idun-project/idun-cartridge/doc/330_112927.jpg

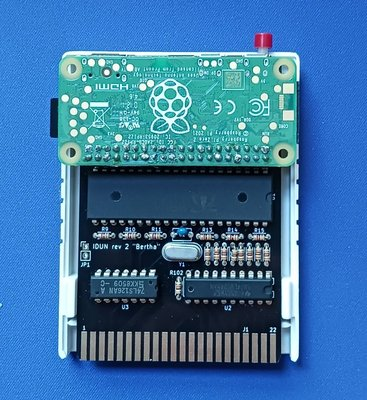
doc/330_112927.jpg
