idun-project/idun-cartridge/cbm/sys/acecall.asm

; Idun Kernel, Copyright ©2023 Brian Holdsworth
; This is free software, released under the MIT License.
;
; Original version from the ACE-128/64 system,
; by Craig Bruce, 1992-97 (http://csbruce.com/cbm/ace/)
;
; Main file/dir/other system calls

rtsErrIllegalDevice = *
   lda #aceErrIllegalDevice
   jmp rtsCarryErrno

;====== file calls ======

;*** open( zp=filenameZ, .A=mode["r","w","a","W","A"] ) : .A=fcb

aceOpenOverwrite = *
   +ldaSCII "w"
   jsr open
   bcs +
   rts
+  ldy errno
   cpy #aceErrFileExists
   beq +
   sec
-  rts
+  jsr internRemove
   bcs -
   bcc aceOpenWrite   ;.CC guaranteed here (fell through bcs above), effectively 2-byte jmp

aceOpenForceAppend = *
   +ldaSCII "a"
   jsr open
   bcs +
   rts
+  ldy errno
   cpy #aceErrFileNotFound
   beq aceOpenWrite
   sec
   rts

aceOpenWrite = *
   +ldaSCII "w"
   jmp kernFileOpen

;NAME   :  open
;PURPOSE:  open a file
;ARGS   :  (zp) = pathname
;          .A   = file mode ("r", "w", "a", "W", "A", or "C")
;RETURNS:  .A   = file descriptor number
;          .CS  = error occurred flag
;ALTERS :  .X, .Y, errno

openFcb      = syswork+0
openNameScan = syswork+1  ;mioCheckDiskStatus (acemiocbm.asm) reuses this byte
                          ;for its parsed status code once the name scan is done
openMode     = syswork+2
openNameLength = syswork+3
openDevice   = syswork+4
checkStat !byte 0

kernFileOpen = *
internOpen = *
   sta openMode
   +cmpASCII "W"
   bne +
   jmp aceOpenOverwrite
+  +cmpASCII "A"
   bne +
   jmp aceOpenForceAppend
+  +cmpASCII "C"
   bne ++
   jsr getFcb
   bcc +
   rts
+  +ldaSCII "R"
   sta openMode
   lda #cmdlf
   jmp fileOpenCont
++ jsr getLfAndFcb
   bcc fileOpenCont
   rts

   fileOpenCont = *
   sta lftable,x
   lda #$00
   sta eoftable,x
   sta checkStat
   stx openFcb
   jsr getDevice
   sty openNameScan
   ldx openFcb
   sta devtable,x
   sta openDevice
   tax
   ;get sa here
   lda configBuf+0,x
   ;** #0-#1 go to mio
   cmp #2
   bcs +
   jmp mioOpenSa
   ;** #2-#3: nothing else to do, just return the fcb
+  cmp #4
   bcs +
   lda openFcb
   ;clc not needed -- carry is guaranteed clear here (fell through bcs above)
   rts
   ;** check mem-mapper files
+  cmp #5
   bne +
   jmp internTagOpen
   ;** check virtual console
+  cmp #6
   bne +
   jmp pidOpen
   ; IDUN: type #4 and #7+ share this cmdlf/regsave dispatch --
   ; nothing else can reach here (0-3,5,6 all handled above)
+  ldx openFcb
   lda lftable,x
   cmp #cmdlf
   bne ++
   stx regsave+1
   ldx openDevice
   lda configBuf+2,x
   sta openFcb
   jsr pidOpen
   bcc +
   rts
+  lda regsave+1
   rts
++ jmp pidOpen

cmdchClose = *  ;( .X=device, matches cmdchOpen's convention )
   lda configBuf+0,x
   cmp #1
   bne +
   jmp mioCmdchClose
+  lda configBuf+2,x
   sta closeFd
   jmp pidClose


;NAME   :  close
;PURPOSE:  close an open file
;ARGS   :  .A   = File descriptor number
;RETURNS:  .CS  = error occurred flag
;ALTERS :  .A, .X, .Y, errno

closeFd !byte 0

kernFileClose = *
aceClose = *
internClose = *
   tax
   lda lftable,x
   cmp #cmdlf
   bne +
   lda devtable,x  ;cmdchClose now takes .X=device, translate fd->device here
   tax
   jmp cmdchClose
+  lda pidtable,x
   cmp aceProcessID
   beq +
   clc
   rts
+  ldy devtable,x
   stx closeFd
   internCloseCont = *
   lda configBuf+0,y
   ;** #0-#1 go to mio
   cmp #2
   bcs +
   jmp mioClosePath
   ;** #2-#3 just close entry
+  cmp #4
   bcs +
   bcc closeFdEntry ;.CC guaranteed here (fell through bcs above), effectively 2-byte jmp
   ;** check mem-mapper files
+  cmp #5
   bne +
   jsr internTagClose
   jmp closeFdEntry
   ;** IDUN virtual devices by now (type >=#4 except #5, including #6 virtual console)
+  jsr pidClose
   ; fall through to closeFdEntry

   closeFdEntry = *
   ldx closeFd
   lda #lfnull
   sta lftable,x
   clc
   rts

;NAME   :  read
;PURPOSE:  read data from an open file
;ARGS   :  .X   = File descriptor number
;          (zp) = pointer to buffer to store data into
;          .AY  = maximum number of bytes to read
;RETURNS:  .AY  = (zw) = number of bytes actually read in
;          .CS  = error occurred flag
;          .ZS  = EOF reached flag
;ALTERS :  .X, errno

readMaxLen     = syswork+0
readPtr        = syswork+2
readLength     = syswork+6
readFcb        = syswork+8
readDeviceDisk = syswork+9

;*** read( .X=fcb, (zp)=data, .AY=maxLength ) : .AY=(zw)=length, .Z=eof
kernFileRead = *
   sta readMaxLen+0
   sty readMaxLen+1
   stx readFcb
   lda zp+0
   ldy zp+1
   sta readPtr+0
   sty readPtr+1
   lda #0
   sta readLength+0
   sta readLength+1
   lda eoftable,x
   beq +
   jmp readEofExit
+  lda devtable,x
   tax
   lda configBuf+0,x
   ;** #0-#1 go to mio
   cmp #2
   bcs +
   jmp mioReadPath
   ;** check #2 console
+  cmp #2
   bne +
   lda readMaxLen+0
   ldy readMaxLen+1
   ldx readFcb
   jmp conRead
   ;** check #3 null device
+  cmp #3
   bne +
   lda #0
   ldy #0
   sta zw+0
   sty zw+1
   clc
   rts
   ;** check mem-mapper files
+  cmp #5
   bne +
   jmp internTagRead
   ;** check virtual console -- not implemented for read
+  cmp #6
   bne +
   jmp rtsErrIllegalDevice
   ;** IDUN virtual devices (type #4, #7+); nothing else can reach here
+  jmp pidRead

   readEofExit = *
   lda #0
   ldy #0
+  sta zw+0
   sty zw+1
   clc
   rts


;NAME   :  write
;PURPOSE:  write data to an open file
;ARGS   :  .X   = file descriptor number
;          (zp) = pointer to data to be written
;          .AY  = length of data to be written in bytes
;RETURNS:  .CS  = error occurred
;ALTERS :  .A, .X, .Y, errno

writeLength = syswork+0
writePtr    = syswork+2

;*** write( .X=fcb, (zp)=data, .AY=length )
kernFileWrite = *
internWrite = *
   sta writeLength+0
   sty writeLength+1
   lda zp+0
   ldy zp+1
   sta writePtr+0
   sty writePtr+1
   stx regsave+1
   lda devtable,x
   tax
   lda configBuf+0,x
   ;** #0-#1 go to mio
   cmp #2
   bcs +
   jmp mioWritePath
   ;** check console
+  cmp #2
   bne +
   lda writeLength+0
   ldy writeLength+1
   ldx regsave+1
   jmp conWrite
   ;** check null device
+  cmp #3
   bne +
   clc
   rts
   ;** #5-#6: mem-mapper files/virtual console, neither implemented for write;
+  cmp #5
   bcc +
   cmp #7
   bcs +
   jmp rtsErrIllegalDevice
   ;** everything else (type #4, #7+) goes to pidWrite
+  ldx regsave+1
   jmp pidWrite

;NAME   :  seek
;PURPOSE:  seek to file location
;ARGS   :  .X   = file descriptor number
;          .AY  = desired seek offset from start-of-file
;RETURNS:  .CS  = error occurred
;ALTERS :  .A, .X, .Y, errno

seekPtr       = syswork+0

;*** seek( .X=fcb, .AY=offset )

kernFileLseek = *
   sta seekPtr+0
   sty seekPtr+1
   ldy #0
   lda devtable,x
   tax
   lda configBuf+0,x
   ;seek only suppoorted by mem-mapped files (#5)
   cmp #5
   bne lseekIllegal
   jmp internTagSeek
   lseekIllegal = *
   jmp rtsErrIllegalDevice


;NAME   :  aceFileRemove
;PURPOSE:  delete a file
;ARGS   :  (zp) = pathname
;RETURNS:  .CS  = error occurred flag
;ALTERS :  .A, .X, .Y, errno

removeDevice = syswork+0  ;== renameDevice/chdirDevice below -- acemiocbm.asm's
                           ;mioCmdchTransact relies on this shared location to
                           ;fold its open/send/status/close tail across
                           ;mioRemovePath, mioRenamePath and mioChdirPath
;openNameScan(syswork+1) is set below too, then reused by mioCheckDiskStatus
;for its status code once mioRemovePath has consumed it -- see acemiocbm.asm

;*** aceFileRemove( (zp)=Name )
kernFileRemove = *
internRemove = *
   jsr getDiskDevice     ;bails out of this call on non-disk device
   sta removeDevice
   sty openNameScan
   ; IDUN: Type #1. Call MOS
   cpx #1
   bne +
   jmp mioRemovePath
   ; IDUN: Type #4/7. Replace with acepid.
+  ldx removeDevice
   jmp pidRemove


;NAME   :  aceFileRename
;PURPOSE:  rename a file or directory
;ARGS   :  (zp) = old filename
;          (zw) = new filename
;RETURNS:  .CS  = error occurred flag
;ALTERS :  .A, .X, .Y, errno

renameDevice = syswork+0  ;== removeDevice above/chdirDevice below -- see the
                           ;mioCmdchTransact note at removeDevice's definition
;openNameScan(syswork+1) is set below too, then reused by mioCheckDiskStatus
;for its status code once mioRenamePath has consumed it -- see acemiocbm.asm

;*** aceFileRename( (zp)=OldName, (zw)=NewName )
;*** don't even think about renaming files outside the current directory
kernFileRename = *
   jsr getDiskDevice     ;bails out of this call on non-disk device
   sta renameDevice
   sty openNameScan
   ; IDUN: Type #1. Call MOS
   cpx #1
   bne +
   jmp mioRenamePath
   ; IDUN: Type #4/7. Replace with acepid.
+  ldx renameDevice
   jmp pidRename


;NAME   :  aceFileBload/aceFileBkload
;PURPOSE:  binary load
;ARGS   :  .X   = RAM bank (0-3 *aceFileBkload only*)
;          (zp) = pathname
;          .AY  = address to load file
;          (zw) = highest address that file may occupy, plus one
;RETURNS:  .AY  = end address of load, plus one
;          .CS  = error occurred flag
;ALTERS :  .X, errno
bloadAddress = syswork
bloadFilename= syswork+2
bloadDevice  = syswork+8
bloadBank    = syswork+9

;*** aceFileBkload( .X=Bank (zp)=Name, .AY=Address, (zw)=Limit+1 ) : .AY=End+1
kernFileBkload = *
internBkload = *
   stx bloadBank
   ldx #0
   jmp +
;*** aceFileBload( (zp)=Name, .AY=Address, (zw)=Limit+1 ) : .AY=End+1
kernFileBload = *
internBload = *
   ldx #0
   stx bloadBank
+  stx checkStat
   stx BloadAppflag
   sta bloadAddress+0
   sty bloadAddress+1
   jsr getDevice
   sta bloadDevice
   tax
   clc
   tya
   adc zp+0
   sta bloadFilename+0
   lda zp+1
   adc #0
   sta bloadFilename+1
   ;IDUN: Check prog name not NUL
   ldy #0
   lda (bloadFilename),y
   bne +
   lda #aceErrFileNotFound
   jmp rtsCarryErrno
+  lda configBuf+0,x
   ;** #1 -> mio
   cmp #1
   bne +
   jmp mioBloadPath
   ;** #5 -> tag RAM
+  cmp #5
   bne +
   jmp internTagBload
   ;** #4/#7 -> pid
+  cmp #4
   beq +
   cmp #7
   bne ++
+  jmp pidBload
++ jmp rtsErrIllegalDevice

;*** aceDirStat ( .A=stat, (zp)=path ) : CS=error,errno
;                                .CC=filled aceSharedBuf

miscInfoDevice = syswork+1  ;kernMiscDeviceInfo's (below) returned device
                            ;number; every caller (here, kernFileStat, and
                            ;mioFileStat in acemiocbm.asm) reads it right
                            ;back out before this slot goes back to being
                            ;openNameScan/chdirNameScan. Defined here, ahead
                            ;of kernMiscDeviceInfo's own definition, so ACME
                            ;sees it as zero page from its first use instead
                            ;of sizing a forward-referenced load as absolute
kernDirStat = *
   ldx #"/"
   cmp #$80
   bne +
   ldx #"%"
+  stx cmdPrefix
   jsr kernMiscDeviceInfo
   bcs +
   jmp rtsErrIllegalDevice
+  lda miscInfoDevice
   sta openDevice
   lda #"r"
   sta openMode
   sty openNameScan
   jsr pidCommandSend
   lda #<dstatRespHandler
   ldy #>dstatRespHandler
   jmp pidCommandResponse
dstatRespHandler = *
   jsr pidFlushbuf
   ; UNLISTEN
   lda #$3F
   jsr pidChOut
   ; Read response size
-  jsr pidChIn
   bcs -
   beq +
   tax
   lda #<aceSharedBuf
   ldy #>aceSharedBuf
   jsr kernModemGet
   lda #$00
+  sta aceSharedBuf,x
   rts

;*** aceFileStat ( (zp)=path ) : .AY=file size,.CS=error,errno
;                                .CC=filled aceDirentBuffer

kernFileStat = *
   jsr kernMiscDeviceInfo
   bcc mioFileStatEntry
   lda miscInfoDevice
   sta openDevice
   lda #"r"
   sta openMode
   lda #"#"
   sta cmdPrefix
   sty openNameScan
   jsr pidCommandSend
   lda #<fstatRespHandler
   ldy #>fstatRespHandler
   jmp pidCommandResponse
fstatRespHandler = *
   jsr pidFlushbuf
   ; UNLISTEN
   lda #$3F
   jsr pidChOut
   ; Read response
   lda #<aceDirentBuffer
   ldy #>aceDirentBuffer
   ldx #aceDirentLength
   jsr kernModemGet
   lda aceDirentNameLen
   bne +
   sec
   rts
+  lda aceDirentBytes+0
   ldy aceDirentBytes+1
   rts

;-- fstatFcb: scratch shared with mioFileStat (acemiocbm.asm); kernDirRead
;   does not touch syswork+3
fstatFcb = syswork+3
mioFileStatEntry = *
   jmp mioFileStat

;-- fcbSetup: allocate FCB; fill lftable/devtable/eoftable/satable/openFcb
;   ( openDevice=set ) : .X=fcb, .CS=error
fcbSetup = *
   jsr getLfAndFcb
   bcs +
   sta lftable,x
   lda openDevice
   sta devtable,x
   lda #0
   sta eoftable,x
   sta satable,x
   stx openFcb
+  rts

;*** aceFileIoctl ( .X=virt. device, (zp)=io cmd ) : .CS=error,errno

kernFileIoctl = *
   stx openDevice
   +ldaSCII "w"
   sta openMode
   lda #"="
   sta cmdPrefix
   lda #0
   sta openNameScan
   jsr pidCommandSend
   jmp pidCommandFinish

;*** aceFileFdswap( .X=Fcb1, .Y=Fcb2 )

kernFileFdswap = *
   lda lftable,x
   pha
   lda lftable,y
   sta lftable,x
   pla
   sta lftable,y
   lda devtable,x
   pha
   lda devtable,y
   sta devtable,x
   pla
   sta devtable,y
   lda satable,x
   pha
   lda satable,y
   sta satable,x
   pla
   sta satable,y
   lda eoftable,x
   pha
   lda eoftable,y
   sta eoftable,x
   pla
   sta eoftable,y
   lda pidtable,x
   pha
   lda pidtable,y
   sta pidtable,x
   pla
   sta pidtable,y
   ; IDUN: also fix up fileinfoTable
   jmp pidFdswap

;====== directory calls ======

;*** aceDirOpen( (zp)=deviceName ) : .A=fcb

kernDirOpen = *
   lda #false
   sta checkStat
   jsr getDiskDevice     ;bails out of this call on non-disk device
   sta openDevice
   sty openNameScan
   cpx #1               ;IEC device?
   bne +                ;no: virtual
   jmp mioDirOpenRoot
+  jsr fcbSetup         ;virtual: allocate FCB then dispatch
   bcc +
   rts
+  jmp pidDirOpen

;*** aceDirClose( ... ) : ...

kernDirClose = *
   tax
   lda pidtable,x
   cmp aceProcessID
   beq +
   clc
   rts
+  stx closeFd
   ldy devtable,x
   jmp internCloseCont

;*** aceDirRead( .X=fcb ) : .Z=eof, aceDirentBuffer=data

kernDirRead = *
   ; ensure aceDirentBytes is zero
   lda #0
   ldy #3
-  sta aceDirentBytes,y
   dey
   bpl -
   ldy devtable,x
   lda configBuf+0,y
   ;fcb's device always came from kernDirOpen's getDiskDevice call, so it's
   ;guaranteed to be type #1, #4 or #7 here -- anything not #1 is acepid's
   cmp #1
   bne +
   jmp mioDirRead
+  jmp pidDirRead

;*** aceDirIsdir( (zp)=FilenameZ ) : .A=Dev, .X=isDisk, .Y=isDir

kernDirIsdir = *
   jsr getDevice
   pha
   tax
   lda configBuf+0,x
   cmp #4
   bne +
   ldx #false
   jmp ++
+  cmp #1
   beq +
   cmp #7
   beq +
   ldx #false
   ldy #false
   jmp isDirExit
+  ldx #true
++ ldy #255
-  iny
   lda (zp),y
   bne -
   dey
   lda (zp),y
   ldy #true
   +cmpASCII ":"
   beq isDirExit
   ldy #false

   isDirExit = *
   pla
   rts

;*** aceDirChange( (zp)=DirName, .A=flags($80=home,$40=parent) )

chdirDevice = syswork+0  ;== removeDevice/renameDevice above -- see the
                          ;mioCmdchTransact note at removeDevice's definition
chdirNameScan = syswork+1  ;reused by mioCheckDiskStatus for its status code
                            ;once mioChdirPath has consumed it -- see acemiocbm.asm
chdirParent !byte $5f,0

kernDirChange = *
internDirChange = *
   cmp #$40
   bne +
   lda #<chdirParent
   ldy #>chdirParent
   sta zp+0
   sty zp+1
   jmp ++
+  cmp #$80
   bne ++
   lda #<configBuf+$80
   ldy #>configBuf+$80
   sta zp+0
   sty zp+1
++ jsr getDiskDevice     ;bails out of this call on non-disk device
   sty chdirNameScan
   sta chdirDevice
   ;getDiskDevice guarantees type #1, #4 or #7 here -- anything not #1 is
   ;acepid's (virtual drives/floppies)
   cpx #1
   bne +
   jmp mioChdirPath
+  ldx chdirDevice
   jmp pidChDir

;-- chdirSetName: commit chdirDevice as the new current directory; shared by
;   the IEC path (mioChdirPath, acemiocbm.asm) and pidChDir (acepid.asm)
;   ( chdirDevice=set ) : .CC
chdirSetName = *
   lda chdirDevice
   sta aceCurrentDevice
   lsr
   lsr
   ora #$40
   sta aceCurDirName+0
   +ldaSCII ":"
   sta aceCurDirName+1
   lda #0
   sta aceCurDirName+2
   clc
   rts

;*** aceIecCommand( (zp)=Command )

kernIecCommand = *
   jmp mioIecCommand

;*** aceDirName( .A=sysdir, (zp)=buf, .Y=assignLen ) : buf, .Y=len
;***   .A : 0=curDir, 1=homedir, 2=execSearchPath, 3=configSearchPath, 4=tempDir
;***   .A : $80+above: assign directory

dirnamePath   !byte 0
dirnameSet    !byte 0
dirnameSetLen !byte 0

kernDirName = *
   ldx #$00
   cmp #$80
   bcc +
   sty dirnameSetLen
   ldx #$ff
+  stx dirnameSet
   and #$07
   ldx #$ff
   cmp #2
   bne +
   ldx #$e0
   stx dirnamePath
   ldy #>configBuf
   jmp ++
+  cmp #4
   bne +
   ldx #$ec
   stx dirnamePath
   ldy #>configBuf
   jmp ++
+  ldx #$00
   stx dirnamePath
   ldx #<aceCurDirName
   ldy #>aceCurDirName
++ stx syswork+0
   sty syswork+1
   bit dirnameSet
   bmi dirnameSetCopy
   ldy #0
-  lda (syswork+0),y
   sta (zp),y
   beq +
   iny
   bne -
+  bit dirnamePath
   bpl +
   iny 
   lda (syswork+0),y
   bne -
   sta (zp),y
+  rts

   dirnameSetCopy = *
   ldy #0
-  lda (zp),y
   sta (syswork+0),y
   iny
   cpy dirnameSetLen
   bcc -
   rts

;====== time calls ======

;*** aceTimeGetDate( (.AY)=dateString )  fmt:YY:YY:MM:DD:HH:MM:SS:TW
;                                             0  1  2  3  4  5  6  7

prevHour !byte 0

kernTimeGetDate = *
internGetDate = *
   php
   sei
   sta syswork+$e
   sty syswork+$f
   ldy #3
-  lda aceDate,y
   sta (syswork+$e),y
   dey
   bpl -
   ldy #4
   lda cia1+$b
   bpl +
   and #$1f
   sed
   clc
   adc #$12
   cld
+  cmp #$12
   bne +
   lda #$00
+  cmp #$24
   bne +
   lda #$12
+  sta (syswork+$e),y
   iny
   lda cia1+$a
   sta (syswork+$e),y
   iny
   lda cia1+$9
   sta (syswork+$e),y
   iny
   lda cia1+$8
   asl
   asl
   asl
   asl
   ora aceDOW
   sta (syswork+$e),y
   ;** check for increment date
   ldy #4
   lda (syswork+$e),y
   cmp prevHour
   sta prevHour
   bcs +
   ldy #3
   lda aceDate,y
   sed
   clc
   adc #$01
   cld
   sta aceDate,y
   sta (syswork+$e),y
   ;** exit
+  plp
   clc
   rts

;*** aceTimeSetDate( (.AY)=dateString )

kernTimeSetDate = *
   sta syswork+0
   sty syswork+1
   ldy #3
-  lda (syswork),y
   sta aceDate,y
   dey
   bpl -
   ldy #4
   lda (syswork),y
   sta prevHour
   cmp #$13
   bcc +
   sed
   sec
   sbc #$12
   cld
   ora #$80
+  sta cia1+$b
   iny
   lda (syswork),y
   sta cia1+$a
   iny
   lda (syswork),y
   sta cia1+$9
   iny
   lda (syswork),y
   lsr
   lsr
   lsr
   lsr
   sta cia1+$8
   lda (syswork),y
   and #$07
   sta aceDOW
   rts


;====== miscellaneous calls ======

;*** aceMiscUtoa( $0+X=value32, (zp)=buf, .A=minLen ) : buf, .Y=len

utoaBin = syswork+2     ;(4)
utoaBcd = syswork+6     ;(5)
utoaFlag = syswork+11   ;(1)
utoaLen = syswork+12    ;(1)
utoaPos = syswork+13    ;(1)
utoaInitOff !byte 0      ;(1)

kernMiscUtoa = *
   ldy #0
   sty utoaInitOff
   cmp #0
   bne +
   lda #1
+  cmp #11
   bcc +
   sec
   sbc #10
   sta utoaInitOff
   ;.y == 0
   +ldaSCII " "
-  sta (zp),y
   iny
   cpy utoaInitOff
   bcc -
   lda #10
+  sta utoaLen
   sec
   lda #10
   sbc utoaLen
   sta utoaLen
   ldy #0
-  lda 0,x
   sta utoaBin,y
   inx
   iny
   cpy #4
   bcc - 
   ldx #4
   lda #0
-  sta utoaBcd,x
   dex
   bpl -
   sta utoaFlag
   ldy #32
   sed

   utoaNextBit = *
   asl utoaBin+0
   rol utoaBin+1
   rol utoaBin+2
   rol utoaBin+3
   ldx #4
-  lda utoaBcd,x
   adc utoaBcd,x
   sta utoaBcd,x
   dex
   bpl -
   dey
   bne utoaNextBit
   cld
   
   lda #10
   sta utoaPos
   ldx #0
   ldy utoaInitOff
-  lda utoaBcd,x
   jsr utoaPutHex
   inx
   cpx #5
   bcc -
   lda #0
   sta (zp),y
   rts

   utoaPutHex = *
   pha
   lsr
   lsr
   lsr
   lsr
   jsr utoaPutDigit
   pla
   and #$0f

   utoaPutDigit = *
   dec utoaPos
   beq utoaForceDigit
   cmp utoaFlag
   bne utoaForceDigit
   dec utoaLen
   bmi +
   rts
+  lda #$20
   bne utoaPoke
   utoaForceDigit = *
   ora #$30
   sta utoaFlag
   
   utoaPoke = *
   sta (zp),y
   iny
   rts


;*** aceMiscSysType () : .A=model, .X=int. banks, .Y=ERAM banks
;                        .sw+0=vdc mem.
kernMiscSysType = *
   ldx aceInternalBanks
   ldy aceEramBanks
   lda configBuf+$aa
   sta syswork+0
   lda winDriver
   lsr
   lsr
   lsr
   lsr
   ora aceSystemType
   rts

;*** aceMiscDeviceInfo( (zp)=path: .A=iec addr,.X=type,.Y=scan pos
;                                  sw=flags,sw+1=device,.CS=virt.drv )
;   ( miscInfoDevice=sw+1 is aliased above, ahead of kernDirStat )
kernMiscDeviceInfo = *
   jsr getDevice
   sty syswork+2
   sta miscInfoDevice
   tay
   lda configBuf+3,y
   sta syswork+0
   lda configBuf+0,y
   tax
   lda configBuf+1,y
   ldy syswork+2
   cpx #7
   beq +
   cpx #4
   bne ++
+  sec
   rts
++ clc
   rts

;*** aceDirAssign ( (zp)=path .X=device ) : .CS=error
kernDirAssign = *
   stx regsave+1
   jsr getDevice
   sty openNameScan
   tax
   jsr pidOpenDir
   bcc +
   rts
+  ldx regsave+1
   +ldaSCII "w"
   jmp pidMount

;*** aceMountImage ( (zp)=image file .X=device, .A=R/W flag)
;                    : .CS=error,errno
kernMountImage = *
   sta regsave+0
   stx regsave+1
   jsr open
   bcc +
   rts
+  pha            ;store image file fd
   ldx regsave+1
   lda regsave+0
   jsr pidMount
   pla
   php
   jsr close      ;close image file
   plp
   bcs +
   lda #0
-  sta errno
   rts
+  lda #aceErrFileTypeMismatch
   jmp -

;*** aceFileCopyHost ( .A=src Fcb, .X=dest Fcb) : .CS=error,errno
; Prerequisites:
; 1. Both source file and destination must be virtual disk files (type #4/7)
; 2. Source file must be valid open'd Fcb
; 3. Destination must be valid, open'd Command Channel (Lfn #31) Fcb
kernCopyHost = *
   jmp pidCopyLocal   

;*** aceTurboCtl ( .A=index, .CS=set) : .A=index, .ZS=none
; The turbo index is a value from 0-15 that maps to a MHz
; speed for the C64U. Bit 7 may also be set in the index to
; disable VIC-II bad line cycle stealing, but this is usually
; not recommended! 
; If you only want to read the current index, then call with
; .CC.
; If the turbo ability appears unavailable or disabled, then
; .Z flag is set in return.
kernTurboCtl = *
   bcs +
-  lda $d031
   cmp #$ff
   rts
+  bit aceTurboCpuFlag
   bmi +
   lda #0
   rts
+  sta $d031
   jmp -

;====== support functions ======

;*** getDevice( zp=filenameZ ) : .A=device, .Y=scanPos

getDevice = *
   ldy #0
   lda (zp),y
   beq useDefault
   ldy #1
   lda (zp),y
   +cmpASCII ":"
   bne useDefault
   ldy #0
   lda (zp),y
   ldy #2
   +cmpASCII "."
   bne +
   lda aceCurrentDevice
   jmp gotDev
+  and #$1f
   asl
   asl
   jmp gotDev
   
   useDefault = *
   lda aceCurrentDevice
   ldy #0

   gotDev = *
   rts

getFcb = *
   ldx #0
-  lda lftable,x
   bmi +
   inx
   cpx #fcbCount
   bcc -
   lda #aceErrTooManyFiles
   jmp rtsCarryErrno
+  lda aceProcessID
   sta pidtable,x
   rts
   
getLfAndFcb = * ;() : .X=fcb, .A=lf
   jsr getFcb
   bcc +
   rts
   openLfSearch = *
+  inc newlf
   lda newlf
   and #$1e    ;Lfn=30/31 reserved for block load & commands
   sec
   sbc #1
   ldy #fcbCount-1
-  cmp lftable,y
   beq openLfSearch
   dey
   bpl -
   clc
   rts

getDiskDevice = *  ;( (zp)=devname ) : .A=device, .Y=scan, .X=dev_t, .CC=isDisk
   ; on failure this pops its own return address and bails out of
   ; the *caller* too (.CS/errno set) - callers just "jsr getDiskDevice"
   ; with no bcc/rts needed; only reachable on success
   jsr getDevice
   pha
   tax
   lda configBuf+0,x
   cmp #1
   bne +
-  tax
   pla
   clc
   rts
+  cmp #4
   beq -
   cmp #7
   beq -
   pla                     ;discard saved device idx
   ; not a disk: pop our own return address so this rts drops
   ; straight back to our caller's caller, bailing it out too
   pla
   pla
   lda #aceErrDiskOnlyOperation
   jmp rtsCarryErrno


;┌────────────────────────────────────────────────────────────────────────┐
;│                        TERMS OF USE: MIT License                       │
;├────────────────────────────────────────────────────────────────────────┤
;│ Copyright (c) 2023 Brian Holdsworth                                    │
;│                                                                        │
;│ Permission is hereby granted, free of charge, to any person obtaining  │
;│ a copy of this software and associated documentation files (the        │
;│ "Software"), to deal in the Software without restriction, including    │
;│ without limitation the rights to use, copy, modify, merge, publish,    │
;│ distribute, sublicense, and/or sell copies of the Software, and to     │
;│ permit persons to whom the Software is furnished to do so, subject to  │
;│ the following conditions:                                              │
;│                                                                        │
;│ The above copyright notice and this permission notice shall be         │
;│ included in all copies or substantial portions of the Software.        │
;│                                                                        │
;│ THE SOFTWARE IS PROVIDED "AS IS", WITHOUT WARRANTY OF ANY KIND         │
;│ EXPRESS OR IMPLIED, INCLUDING BUT NOT LIMITED TO THE WARRANTIES OF     │
;│ MERCHANTABILITY, FITNESS FOR A PARTICULAR PURPOSE AND NONINFRINGEMENT. │
;│ IN NO EVENT SHALL THE AUTHORS OR COPYRIGHT HOLDERS BE LIABLE FOR ANY   │
;│ CLAIM, DAMAGES OR OTHER LIABILITY, WHETHER IN AN ACTION OF CONTRACT,   │
;│ TORT OR OTHERWISE, ARISING FROM, OUT OF OR IN CONNECTION WITH THE      │
;│ SOFTWARE OR THE USE OR OTHER DEALINGS IN THE SOFTWARE.                 │
;└────────────────────────────────────────────────────────────────────────┘
