idun-project/idun-cartridge/cbm/cmd/copy.asm

;'copy' cmd: copy files from source to dest device
;
;Copyright© 2023 Brian Holdsworth
; This is free software, released under the MIT License.
;
; Source and destination devices may be either native or
; virtual drives, but cannot be the same device.
;
; Original version from the ACE-128/64 system,
; by Craig Bruce, 1992-97 (http://csbruce.com/cbm/ace/)
;
;@see usemsg

!source "sys/acehead.asm"
!source "sys/acemacro.asm"
* = aceToolAddress

jmp copymain
!byte aceID1,aceID2,aceID3
!byte 64,0  ;** stack,reserved

;*** global declarations

libwork = $60
chrQuote = $22
overwriteAllFlag !byte 0
insertHeaderFlag !byte 0
abortFlag        !byte 0
;start with assuming src and dest are IEC devices
virtualDevIn     !byte 0
virtualDevOut    !byte 0

;*** zero page vars
virtualFileSz    = 4 ;(2)
copyInFile       = 6 ;(1)
copyOutFile      = 7 ;(1)
scanPos          = 8 ;(1)
copyInDevice     = 9 ;(1)
copyInName       = 10 ;(2)
copyOutName      = 12 ;(2)
copyOpenName     = 14 ;(2)
copyArg          = 16 ;(2)
lastArg          = 18 ;(2)
baseArg          = 20 ;(1)
cpErrno          = 22 ;(4)
copyFileType     = 26 ;(1)

copyUsageErrorMsg = *
!pet "usage: copy [/h] <src> <dest> -or-",chrCR
!pet "       copy [/f] <src1> [src2..srcN] <dev:>",chrCR
!pet "Note: src and dest NOT same device",chrCR
!pet "[/h] to add addr header to dest PRG",chrCR
!pet "[/f] to force overwrite existing dest",chrCR,0

;===copy===
copymain = *
   lda #0
   sta overwriteAllFlag
   sta insertHeaderFlag
   sta abortFlag
   ;** check for at least three arguments
   lda aceArgc+1
   bne +
   lda aceArgc
   cmp #3
   bcs +
   beq +
   jmp copyUsageError
   ;** check for first argument option
   ;   either /f or /h
+  lda #1
   sta baseArg
   lda #1
   ldy #0
   jsr getarg
   ldy #0
   lda (zp),y
   cmp #"/"
   bne ++
   iny
   lda (zp),y
   +cmpASCII "f"
   beq +
   +cmpASCII "h"
   bne copyUsageError
   lda #$ff
   sta insertHeaderFlag
   inc baseArg
   jmp ++
+  lda #$ff
   sta overwriteAllFlag
   inc baseArg
   ;** check if destination is a directory
++ jsr getLastArg
   jsr aceDirIsdir
   cpy #0
   beq +
   jmp copyToDir
   ;** check for exactly three parameters
+  lda aceArgc+1
   bne copyUsageError
   sec
   lda aceArgc
   sbc baseArg
   cmp #2
   bne copyUsageError
   ;** get buffer parameters
   lda baseArg
   ldy #0
   jsr getarg
   lda zp
   ldy zp+1
   sta copyInName
   sty copyInName+1
   inc baseArg
   lda baseArg
   ldy #0
   jsr getarg
   ;** if /h is used, check if outputting to PRG
   lda insertHeaderFlag
   bpl ++
   ldy #0
-  iny 
   lda (zp),y
   bne -
   dey
   lda (zp),y
   +cmpASCII "p"
   beq +
   lda #0
   sta insertHeaderFlag
   jmp ++
+  dey
   lda (zp),y
   +cmpASCII ","
   beq ++
   lda #0
   sta insertHeaderFlag
++ lda zp
   ldy zp+1
   sta copyOutName
   sty copyOutName+1
   jsr copyfile
   rts

copyUsageError = *
   lda #<copyUsageErrorMsg
   ldy #>copyUsageErrorMsg
   ldx #stderr
   jsr fputs
   rts

copyfile = *
   ;** open files
   lda copyInName
   ldy copyInName+1
   sta zp
   sty zp+1
   jsr aceMiscDeviceInfo
   lda syswork+1
   sta copyInDevice
   ;** save virtual flag before aceFileStat clobbers carry
   lda #0
   bcc +
   lda #1
+  sta virtualDevIn
   jsr aceFileStat        ;A=lo filesz (virtual), Y=hi; fills aceDirentType
   sta virtualFileSz      ;save lo size (only meaningful if virtual)
   sty virtualFileSz+1   ;save hi size
   jsr copyDetectType     ;normalizes aceDirentType → copyFileType
   lda virtualDevIn
   beq copyFileIEC
   ;source is virtual device
   lda copyInName
   ldy copyInName+1
   sta zp
   sty zp+1
   lda #"b"
   jmp copyFileOpen
copyFileIEC = *
   lda aceDirentType
   pha
   lda copyInName
   ldy copyInName+1
   sta zp
   sty zp+1
   pla
copyFileOpen = *
   jsr open
   bcc +
   lda copyInName
   ldy copyInName+1
   jmp copyOpenError
+  sta copyInFile
copyfileOutput = *
   lda copyOutName
   ldy copyOutName+1
   sta zp
   sty zp+1
   ; checking src/dest are diff devices
   jsr aceMiscDeviceInfo
   lda syswork+1
   cmp copyInDevice
   beq copyUsageError
   jsr aceMiscDeviceInfo
   bcc +
   lda #1
   sta virtualDevOut
   and virtualDevIn
   beq +
   +ldaSCII "C"   ;open Command channel
   jmp ++
+  lda virtualDevOut
   bne copyOutVirtual
   jsr copyBuildTypedName  ;IEC dest: decorate name with file type
copyOutVirtual = *
   +ldaSCII "W"
++ jsr open
   bcc copyWriteOk
   lda errno
   cmp #aceErrFileExists
   beq +
-  lda copyInFile
   jsr close
   lda copyOutName
   ldy copyOutName+1
   jmp copyOpenError
+  jsr copyAskOverwrite
   beq +
   lda copyInFile
   jsr close
   sec
   rts
+  jsr copyRemoveOutfile
   jmp copyfileOutput

   copyWriteOk = *
   sta copyOutFile
   lda virtualDevIn
   and virtualDevOut
   beq +
   lda copyInFile
   ldx copyOutFile
   jsr aceFileCopyHost
   jmp copyFileFinish
+  jsr copyFileContents
   copyFileFinish = *
   lda copyOutFile
   jsr close
   lda copyInFile
   jsr close
   rts

copyAskOverwrite = *  ;() : .CS=quit, .EQ=yes, .NE=no
   lda overwriteAllFlag
   beq +
   lda #0
   rts
   copyAskCont = *
+  lda #<copyAskOverwriteMsg
   ldy #>copyAskOverwriteMsg
   jsr puts
   lda copyOutName
   ldy copyOutName+1
   jsr puts
   lda #<copyAskOverwriteMsg2
   ldy #>copyAskOverwriteMsg2
   jsr puts
   jsr getchar
   cmp #chrCR
   beq copyAskCont
   pha
-  jsr getchar
   cmp #chrCR
   bne -
   pla
   +cmpASCII "q"
   bne +
-  lda #$ff
   sta abortFlag
   sec
   rts
+  +cmpASCII "Q"
   beq -
   +cmpASCII "a"
   bne +
-  lda #$ff
   sta overwriteAllFlag
   +ldaSCII "y"
+  +cmpASCII "A"
   beq -
   +cmpASCII "y"
   beq +
   +cmpASCII "Y"
+  clc
   rts
   copyAskOverwriteMsg = *
   !pet "Overwrite ",chrQuote,0
   copyAskOverwriteMsg2 = *
   !pet chrQuote," (y/n/a/q)? ",0

copyRemoveOutfile = *
   lda copyOutName
   ldy copyOutName+1
   sta zp
   sty zp+1
   jsr aceFileRemove
   rts

copyFileContents = *
   ;** check whether adding addr header
   lda insertHeaderFlag
   bpl copyFileContinue
   lda #<aceToolAddress
   sta zp
   lda #>aceToolAddress
   sta zp+1
   ldy #0
   lda #2
   ldx copyOutFile
   jsr write
   bcc copyFileContinue
   jmp copyFileError
   ;** copy file contents
   copyFileContinue = *
   lda #<copyBufferPtr
   ldy #>copyBufferPtr
   sta zp
   sty zp+1
   jsr checkstop
   jsr copyBlockSz   
   ldx copyInFile
   jsr read
   bcs ++
   sta zw
   sty zw+1
   ora zw+1
   beq +
   jsr checkstop
   lda zw
   ldy zw+1
   ldx copyOutFile
   jsr write
   bcs ++
   lda zw+1
   beq +
   jmp copyFileContinue
+  rts
++ jmp copyFileError
   
   copyBlockSz = *
   lda virtualDevIn
   bne +
   lda #0
   ldy #1
   rts
+  lda virtualFileSz
   ldy virtualFileSz+1
   beq +
   dec virtualFileSz+1
   lda #0
   ldy #1
+  rts

   copyOpenError = *
   ldx errno
   stx cpErrno+0
   sta copyOpenName
   sty copyOpenName+1
   lda #<copyOpenErrorMsg1
   ldy #>copyOpenErrorMsg1
   ldx #stderr
   jsr fputs
   lda copyOpenName
   ldy copyOpenName+1
   ldx #stderr
   jsr fputs
   lda #<copyOpenErrorMsg2
   ldy #>copyOpenErrorMsg2
   ldx #stderr
   jsr fputs
   lda #0
   sta cpErrno+1
   sta cpErrno+2
   sta cpErrno+3
   lda #<cpNumbuf
   ldy #>cpNumbuf
   sta zp+0
   sty zp+1
   ldx #cpErrno
   lda #1
   jsr aceMiscUtoa
   lda #<cpNumbuf
   ldy #>cpNumbuf
   ldx #stderr
   jsr fputs
   lda #<copyOpenErrorMsg3
   ldy #>copyOpenErrorMsg3
   ldx #stderr
   jsr fputs
   rts

cpNumbuf !fill 12,0
   copyOpenErrorMsg1 = *
   !pet "Error opening file ",chrQuote,0
   copyOpenErrorMsg2 = *
   !pet chrQuote,", code ",0
   copyOpenErrorMsg3 = *
   !pet chrCR,0

   copyFileError = *
   lda #<copyFileErrorMsg
   ldy #>copyFileErrorMsg
   ldx #stderr
   jmp fputs
   copyFileErrorMsg = *
   !pet "File data error!",chrCR,0

copyVirtualContents = *
   rts

copyToDir = *
   lda baseArg
   ldy #0
   sta copyArg+0
   sty copyArg+1
-  lda aceArgc+0
   ldy aceArgc+1
   sec
   sbc #1
   bcs +
   dey
+  cmp copyArg+0
   bne +
   cpy copyArg+1
   beq copyToDirExit
+  jsr checkstop
   lda copyArg+0
   ldy copyArg+1
   jsr getarg
   lda zp+0
   ldy zp+1
   sta copyInName+0
   sty copyInName+1
   jsr copyFileToDir
   lda abortFlag
   bne copyToDirStopped
   inc copyArg+0
   bne +
   inc copyArg+1
+  jmp -

copyToDirExit = *
   rts

checkstop = *
   jsr aceConStopkey
   bcs +
   rts
copyToDirStopped = *
+  lda #<stoppedMsg
   ldy #>stoppedMsg
   jsr eputs
   lda #1
   ldx #0
   jmp aceProcExit

   stoppedMsg = *
   !pet "<Stopped>",chrCR,0

copyFileToDir = *
   ;** generate output file name
   jsr getLastArg
   ldy #0
-  lda (zp),y
   beq +
   sta copyNameBuf,y
   iny
   bne -
+  tya
   tax
   ;** extract basename
   ldy #0
   sty scanPos
-  lda (copyInName),y
   beq +
   +cmpASCII ":"
   bne basenameNext
   iny
   sty scanPos
   dey
   basenameNext = *
   iny
   bne -

+  ldy scanPos
-  lda (copyInName),y
   sta copyNameBuf,x
   beq +
   inx
   iny
   bne -
   ;** strip .prg/.usr always; add back when dest is host drive
+  stx scanPos
   jsr copyStripExt
   lda copyInName
   ldy copyInName+1
   sta zp
   sty zp+1
   jsr aceFileStat
   jsr copyDetectType
   lda #<copyNameBuf
   ldy #>copyNameBuf
   sta zp
   sty zp+1
   jsr aceMiscDeviceInfo
   bcc copyFTDSetOut
   jsr copyAddExt
;** copy file
copyFTDSetOut = *
   lda #<copyNameBuf
   ldy #>copyNameBuf
   sta copyOutName+0
   sty copyOutName+1
   jsr copyToDirStatus
   jsr copyfile
   rts

copyStripExt = *
   ;** strip .prg or .usr from end of copyNameBuf
   ;   scanPos = null position (string length)
   lda scanPos
   cmp #4
   bcc copyStripRet
   sec
   sbc #4
   tax
   lda copyNameBuf,x
   +cmpASCII "."
   bne copyStripRet
   inx
   lda copyNameBuf,x
   +cmpASCII "p"
   beq copyStripChkPRG
   +cmpASCII "u"
   bne copyStripRet
   inx
   lda copyNameBuf,x
   +cmpASCII "s"
   bne copyStripRet
   inx
   lda copyNameBuf,x
   +cmpASCII "r"
   bne copyStripRet
   jmp copyStripDo
copyStripChkPRG = *
   inx
   lda copyNameBuf,x
   +cmpASCII "r"
   bne copyStripRet
   inx
   lda copyNameBuf,x
   +cmpASCII "g"
   bne copyStripRet
copyStripDo = *
   lda scanPos
   sec
   sbc #4
   tax
   lda #0
   sta copyNameBuf,x
   stx scanPos
copyStripRet = *
   rts

copyAddExt = *
   ;** append .prg or .usr to copyNameBuf at scanPos; no-op for SEQ
   lda copyFileType
   +cmpASCII "p"
   beq copyAddPRG
   +cmpASCII "u"
   bne copyAddExtRet
   ldx scanPos
   lda #$2e
   sta copyNameBuf,x
   inx
   +ldaSCII "u"
   sta copyNameBuf,x
   inx
   +ldaSCII "s"
   sta copyNameBuf,x
   inx
   +ldaSCII "r"
   sta copyNameBuf,x
   inx
   lda #0
   sta copyNameBuf,x
   rts
copyAddPRG = *
   ldx scanPos
   lda #$2e
   sta copyNameBuf,x
   inx
   +ldaSCII "p"
   sta copyNameBuf,x
   inx
   +ldaSCII "r"
   sta copyNameBuf,x
   inx
   +ldaSCII "g"
   sta copyNameBuf,x
   inx
   lda #0
   sta copyNameBuf,x
copyAddExtRet = *
   rts

copyDetectType = *
   ;** normalize aceDirentType[0] → copyFileType ('P','U', or 'S')
   lda aceDirentType
   +cmpASCII "p"
   beq +
   +cmpASCII "u"
   beq +
   +ldaSCII "s"
+  sta copyFileType
   rts

copyBuildTypedName = *
   ;** copy (zp)=copyOutName to copyNameBuf, append ,<copyFileType>
   ;   sets zp = copyNameBuf for subsequent open call
   ldy #0
-  lda (zp),y
   sta copyNameBuf,y
   beq +
   iny
   bne -
+  lda #$2c          ;','
   sta copyNameBuf,y
   iny
   lda copyFileType
   sta copyNameBuf,y
   iny
   lda #0
   sta copyNameBuf,y
   lda #<copyNameBuf
   ldy #>copyNameBuf
   sta zp
   sty zp+1
   rts

toChars !pet " -> ",0
copyToDirStatus = *
   lda copyInName+0
   ldy copyInName+1
   jsr puts
   lda #<toChars
   ldy #>toChars
   jsr puts
   lda copyOutName+0
   ldy copyOutName+1
   jsr puts
   lda #chrCR
   jsr putchar
   rts

;******** standard library ********
eputs = *
   ldx #stderr
   jmp fputs
puts = *
   ldx #stdout
fputs = *
   sta zp
   sty zp+1
   ldy #$ff
-  iny
   lda (zp),y
   bne -
   tya
   ldy #0
   jmp write

putchar = *
   ldx #stdout
putc = *
   sta putcBuffer
   lda #<putcBuffer
   ldy #>putcBuffer
   sta zp
   sty zp+1
   lda #1
   ldy #0
   jmp write
putcBuffer !byte 0

getchar = *
   ldx #stdin
getc = *
   lda #<getcBuffer
   ldy #>getcBuffer
   sta zp
   sty zp+1
   lda #1
   ldy #0
   jsr read
   beq +
   lda getcBuffer
   rts
+  sec
   rts
getcBuffer !byte 0

;===copy library===
getarg = *
   sty zp+1
   asl
   rol zp+1
   clc
   adc aceArgv+0
   sta zp+0
   lda aceArgv+1
   adc zp+1
   sta zp+1
   ldy #0
   lda (zp),y
   tax
   iny
   lda (zp),y
   stx zp+0
   sta zp+1
   rts

getLastArg = *
   lda aceArgc+0
   ldy aceArgc+1
   sec
   sbc #1
   bcs +
   dey
+  jmp getarg

;===the end===
cpBss = *
copyNameBuf = cpBss+0
copyBufferPtr = copyNameBuf+256

;┌────────────────────────────────────────────────────────────────────────┐
;│                        TERMS OF USE: MIT License                       │
;├────────────────────────────────────────────────────────────────────────┤
;│ Copyright (c) 2023 Brian Holdsworth                                    │
;│                                                                        │
;│ Permission is hereby granted, free of charge, to any person obtaining  │
;│ a copy of this software and associated documentation files (the        │
;│ "Software"), to deal in the Software without restriction, including    │
;│ without limitation the rights to use, copy, modify, merge, publish,    │
;│ distribute, sublicense, and/or sell copies of the Software, and to     │
;│ permit persons to whom the Software is furnished to do so, subject to  │
;│ the following conditions:                                              │
;│                                                                        │
;│ The above copyright notice and this permission notice shall be         │
;│ included in all copies or substantial portions of the Software.        │
;│                                                                        │
;│ THE SOFTWARE IS PROVIDED "AS IS", WITHOUT WARRANTY OF ANY KIND         │
;│ EXPRESS OR IMPLIED, INCLUDING BUT NOT LIMITED TO THE WARRANTIES OF     │
;│ MERCHANTABILITY, FITNESS FOR A PARTICULAR PURPOSE AND NONINFRINGEMENT. │
;│ IN NO EVENT SHALL THE AUTHORS OR COPYRIGHT HOLDERS BE LIABLE FOR ANY   │
;│ CLAIM, DAMAGES OR OTHER LIABILITY, WHETHER IN AN ACTION OF CONTRACT,   │
;│ TORT OR OTHERWISE, ARISING FROM, OUT OF OR IN CONNECTION WITH THE      │
;│ SOFTWARE OR THE USE OR OTHER DEALINGS IN THE SOFTWARE.                 │
;└────────────────────────────────────────────────────────────────────────┘
