idun-project/idun-cartridge/cbm/arcade.app.d/app.asm

;This interface shows the selectable search results
;on the left-hand side of the screen.
ResultsIntf:
	+toolUserIntfCol ~iResults, 22
	lda #0
	sta toolUserStyles
	lda #$00
	sta toolUserColor
	jsr toolUserNode
_node !byte 0,1          ;draw from 0,1
	;21 entries
_row1:
	jsr toolUserGadget        ;1
       !pet $82,"                      ",0
_bytes_per_srch_entry = *-_row1
_row2:
    jsr toolUserGadget        ;2
       !pet 0,"                      ",0
    jsr toolUserGadget        ;3
       !pet 0,"                      ",0
    jsr toolUserGadget        ;4
       !pet 0,"                      ",0
_row5:
    jsr toolUserGadget        ;5
       !pet 0,"                      ",0
    jsr toolUserGadget        ;6
       !pet 0,"                      ",0
    jsr toolUserGadget        ;7
       !pet 0,"                      ",0
    jsr toolUserGadget        ;8
       !pet 0,"                      ",0
    jsr toolUserGadget        ;9
       !pet 0,"                      ",0
    jsr toolUserGadget        ;10
       !pet 0,"                      ",0
_row11:
    jsr toolUserGadget        ;11
       !pet 0,"                      ",0
    jsr toolUserGadget        ;12
       !pet 0,"                      ",0
    jsr toolUserGadget        ;13
       !pet 0,"                      ",0
    jsr toolUserGadget        ;14
       !pet 0,"                      ",0
    jsr toolUserGadget        ;15
       !pet 0,"                      ",0
    jsr toolUserGadget        ;16
       !pet 0,"                      ",0
    jsr toolUserGadget        ;17
       !pet 0,"                      ",0
    jsr toolUserGadget        ;18
       !pet 0,"                      ",0
    jsr toolUserGadget        ;19
       !pet 0,"                      ",0
    jsr toolUserGadget        ;20
       !pet 0,"                      ",0
_row21:
    jsr toolUserGadget        ;21
       !pet 0,"                      ",0
	jsr toolUserEnd
	inc iResults            ;clear redraw
	rts

;This interface shows the selectable program list
;on the right-hand side of the screen.
ProgramsIntf:
	+toolUserIntfCol ~iPrograms, 16
	lda #0
	sta toolUserStyles
	lda #$00
	sta toolUserColor
	jsr toolUserNode
_node2 !byte 23,13			  ;draw from 23,13
	;9 entries
_prg1:
	jsr toolUserGadget        ;1
       !pet $82,"                ",0
_bytes_per_prog_entry = *-_prg1
    jsr toolUserGadget        ;2
       !pet 0,"                ",0
    jsr toolUserGadget        ;3
       !pet 0,"                ",0
    jsr toolUserGadget        ;4
       !pet 0,"                ",0
    jsr toolUserGadget        ;5
       !pet 0,"                ",0
    jsr toolUserGadget        ;6
       !pet 0,"                ",0
    jsr toolUserGadget        ;7
       !pet 0,"                ",0
    jsr toolUserGadget        ;8
       !pet 0,"                ",0
_prg9:
    jsr toolUserGadget        ;9
       !pet 0,"                ",0
	jsr toolUserEnd
	inc iPrograms            ;clear redraw
	rts

appInitialize = *
	;ensure 40-column VIC-II screen only!
    lda #0
    ldx #40
    jsr aceWinScreen
	;init vars
	lda #0
	sta rowc
	sta searchBoxPos
	lda #<_row1
	ldy #>_row1
	sta focusEntry+0
	sty focusEntry+1
	;black border/background
	lda #0
	sta $d020
	sta $d021
	;load custom character set
	lda #<chrsetBrowse
	ldy #>chrsetBrowse
	sta zp
	sty zp+1
	lda aceMemTop
	sta zw
	lda aceMemTop+1
	sta zw+1
	lda #<.charsetBuf
	ldy #>.charsetBuf
	jsr aceFileBload
	bcc +
	jmp exit
+   lda #<.charsetBuf
	ldx #>.charsetBuf
	sta syswork+0
	stx syswork+1
	ldy #5
	lda (syswork+0),y
	tay
	clc
	lda syswork+0
	adc #8
	bcc +
	inx
+   sta syswork+0
	stx syswork+1
	lda #%11100000
	cpy #$00
	beq +
	ora #%00010000
+   ldx #$00
	ldy #40
	jsr aceWinChrset
	clc
	lda syswork+0
	adc #40
	sta syswork+0
	bcc +
	inc syswork+1
+   lda #%10001010
	ldx #$00
	ldy #0
	jsr aceWinChrset
	;copy color RAM
	lda #<$d800
	ldy #>$d800
	sta zp+0		;dest
	sty zp+1
	lda #<screen_colors
	ldy #>screen_colors
	sta syswork+0	;src
	sty syswork+1
	lda #0
	sta syswork+2	;row
--	ldy #39			;col
-	lda (syswork),y
	sta (zp),y
	dey
	bpl -
	inc syswork+2
	lda syswork+2
	cmp #25
	beq +
	lda zp+0
	clc
	adc #40
	sta zp+0
	lda zp+1
	adc #0
	sta zp+1
	lda syswork+0
	clc
	adc #40
	sta syswork+0
	lda syswork+1
	adc #0
	sta syswork+1
	jmp --
	;populate screen/fields
+	lda rowc
	ldx #0
	jsr aceWinPos
	lda #40
	sta syswork+5
	lda #0
	sta syswork+6
	lda #<screen_codes
	ldy #>screen_codes
	sta syswork+2
	sty syswork+3
-	lda #$80
	ldx #40
	jsr aceWinPut
	inc rowc
	lda rowc
	cmp #25
	beq +
	ldx #0
	jsr aceWinPos
	lda syswork+2
	clc
	adc #40
	sta syswork+2
	lda syswork+3
	adc #0
	sta syswork+3
	jmp -
	;setup key handling
+	ldx #<exit
	ldy #>exit
	lda #HotkeyStop
	jsr toolKeysSet
	ldx #<prevPage
	ldy #>prevPage
	lda #HotkeyCtrlUp
	jsr toolKeysSet
	ldx #<nextPage
	ldy #>nextPage
	lda #HotkeyCtrlDown
	jsr toolKeysSet
	ldx #<getRecents
	ldy #>getRecents
	lda #HotkeyF1
	jsr toolKeysSet
	ldx #<getFavorites
	ldy #>getFavorites
	lda #HotkeyF3
	jsr toolKeysSet
	ldx #<setFavorite
	ldy #>setFavorite
	lda #HotkeyF7
	jsr toolKeysSet
	;draw UI
	jsr ResultsIntf
	jmp updateSearchBox
chrsetBrowse !pet "z:chrset-browse",0

checkSearchInput = *
	jsr aceConKeyAvail
	bcc +
	rts
+	cmp #chrBS
	bne ++
	jsr aceConGetkey
	dec searchBoxPos
	bpl +
	ldx #0
	stx searchBoxPos
+	jmp contSearchInput
++	cmp #$20
	bcs +		;check if printable ($20-$5f, $c1-$df)
	sec
	rts
+	cmp #$5f
	bcc ++
	cmp #$c1
	bcs +
	sec
	rts
+	cmp #$df
	bcc ++
	rts
++	jsr aceConGetkey
	ldx searchBoxPos
	cpx #SEARCH_FIELD_SZ
	bne +
	clc
	rts
+	sta search_box,x
	inc searchBoxPos
	contSearchInput = *
	ldx #TKEY
	ldy #ID_SEARCH
	jsr m8_send_event
	lda #<RESULTS_MBOX
	ldy #>RESULTS_MBOX
	jsr m8_wait_mailbox
	clc
	rts

updateSearchBox = *
	lda aceVic40Page
	sta search_box_offs+2
	ldx searchBoxPos
	bne +
	lda #$20
search_box_offs:
	sta $f800+search_box-screen_codes+1
	jmp ++
+	lda #<(search_box-screen_codes)
	ldy #>(search_box-screen_codes)
	sta syswork+0
	sty syswork+1
	lda syswork+1
	clc
	adc aceVic40Page
	sta syswork+1
	lda #<search_box
	ldy #>search_box
	sta syswork+2
	sty syswork+3
	lda #$20
	sta syswork+4
	lda #SEARCH_FIELD_SZ+1
	sta syswork+5
	lda #$c0
	ldy toolWinPalette+0
	jsr aceWinPut	;put text
++	lda #<(search_box-screen_codes)
	ldy #>(search_box-screen_codes)
	clc
	adc searchBoxPos
	sta syswork+0
	tya
	adc aceVic40Page
	sta syswork+1
	lda #$e0
	sta syswork+4
	lda #$c0
	ldx #1
	stx syswork+5
	ldx #0
	ldy toolWinPalette+4
	jsr aceWinPut	;put cursor
	rts

getRecents = *
	lda #HotkeyF1
	jmp sendHotkey
getFavorites = *
	lda #HotkeyF3
sendHotkey = *
	ldx #TKEY
	ldy #ID_HOTKEY
	jsr m8_send_event
	lda #<RESULTS_MBOX
	ldy #>RESULTS_MBOX
	jsr m8_wait_mailbox
	rts
setFavorite = *
	lda #HotkeyF7
	ldx #TKEY
	ldy #ID_HOTKEY
	jmp m8_send_event
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
